openspaceaarhus/ZABLET/doc/image/bc337.jpg

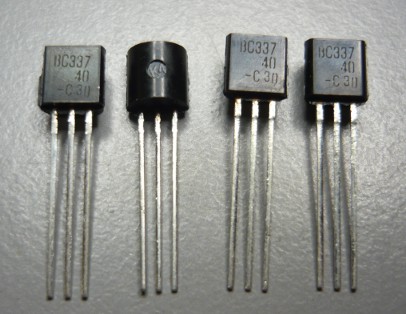
doc/image/bc337.jpg
