openspaceaarhus/ZABLET/doc/image/bc558.jpg

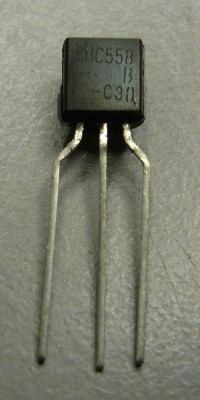
doc/image/bc558.jpg
