openspaceaarhus/ZABLET/doc/image/button.jpg

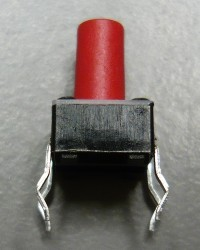
doc/image/button.jpg
