openspaceaarhus/ZABLET/doc/image/case-bottom.jpg

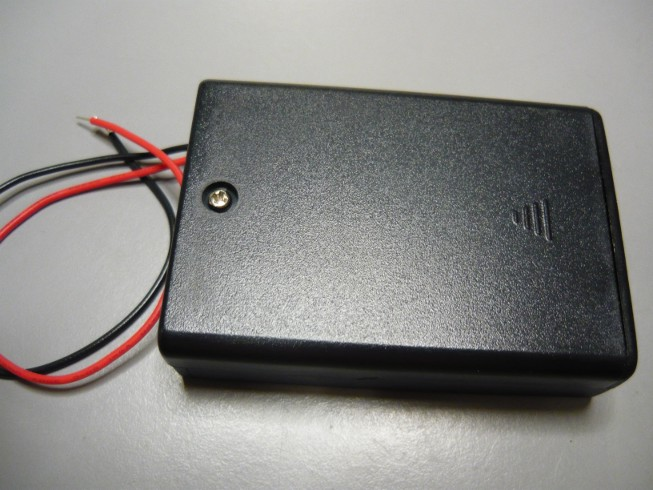
doc/image/case-bottom.jpg
