openspaceaarhus/ZABLET/doc/image/case-inside-loose.jpg

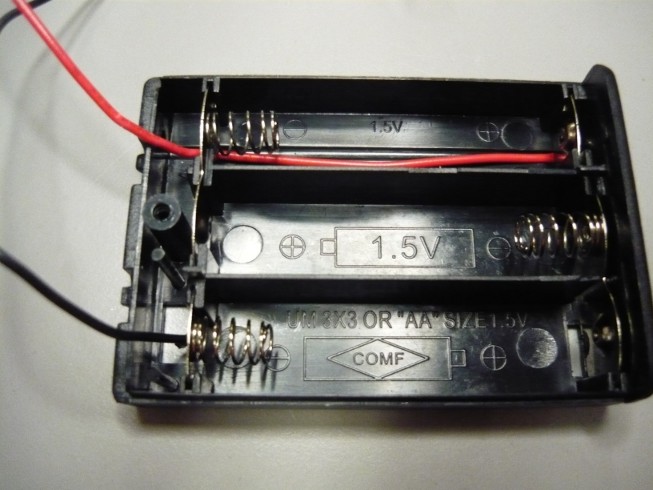
doc/image/case-inside-loose.jpg
