openspaceaarhus/ZABLET/doc/image/case-inside-orig.jpg

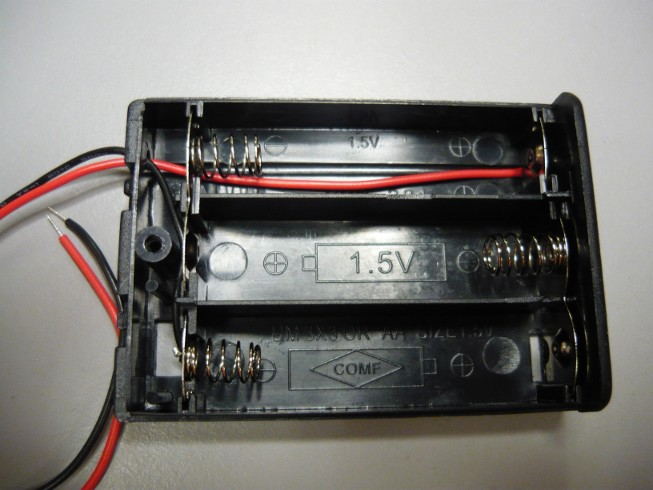
doc/image/case-inside-orig.jpg
