openspaceaarhus/ZABLET/doc/image/case-inside-rerouted.jpg

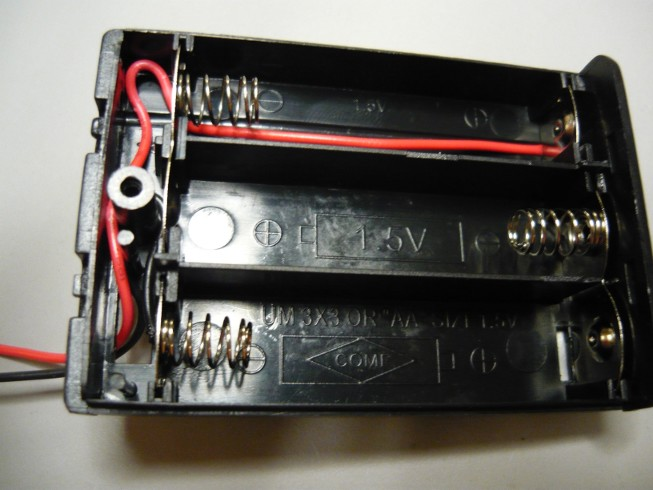
doc/image/case-inside-rerouted.jpg
