openspaceaarhus/ZABLET/doc/image/case-outside-rerouted.jpg

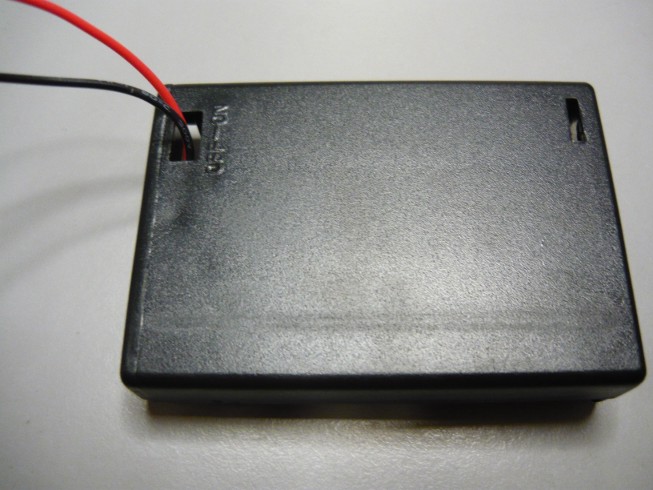
doc/image/case-outside-rerouted.jpg
