openspaceaarhus/ZABLET/doc/image/case-top.jpg

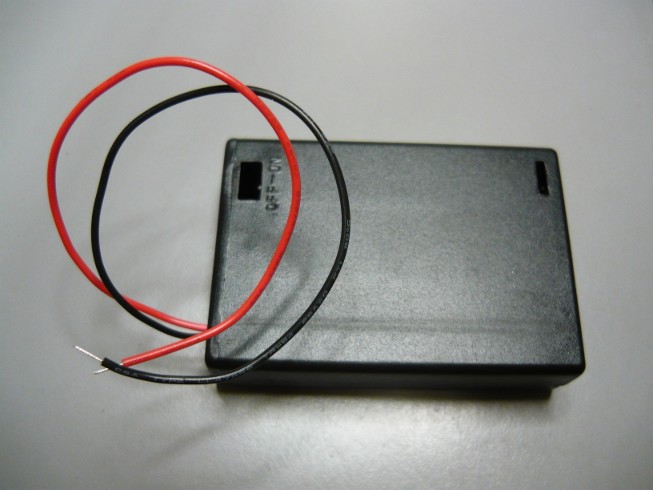
doc/image/case-top.jpg
