openspaceaarhus/ZABLET/doc/image/ceramic-caps.jpg

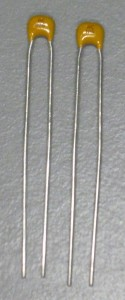
doc/image/ceramic-caps.jpg
