openspaceaarhus/ZABLET/doc/image/elco.jpg

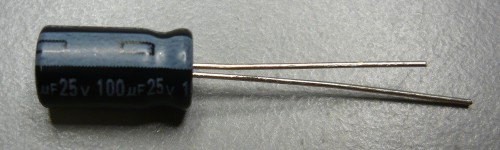
doc/image/elco.jpg
