openspaceaarhus/ZABLET/doc/image/header-6.jpg

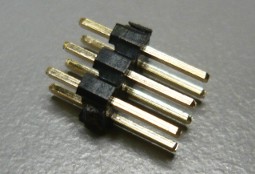
doc/image/header-6.jpg
