openspaceaarhus/ZABLET/doc/image/ir333-h0-spread.png

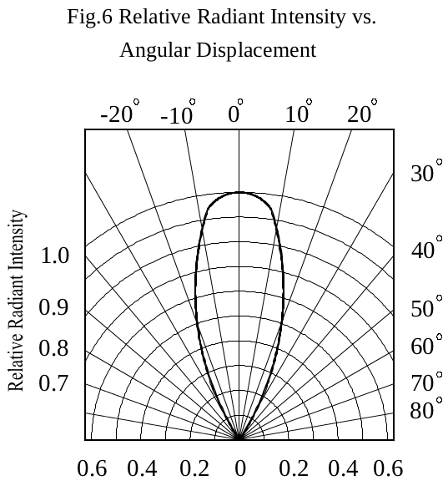
doc/image/ir333-h0-spread.png
