openspaceaarhus/ZABLET/doc/image/ir333a-spread.png

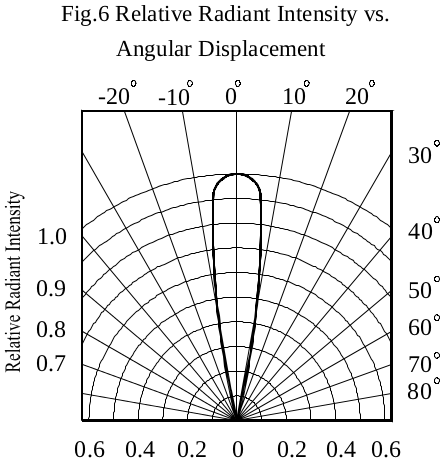
doc/image/ir333a-spread.png
