openspaceaarhus/ZABLET/doc/image/irled-10gr.jpg

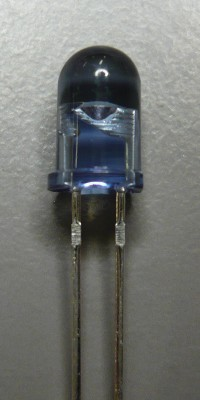
doc/image/irled-10gr.jpg
