openspaceaarhus/ZABLET/doc/image/irled-30gr.jpg

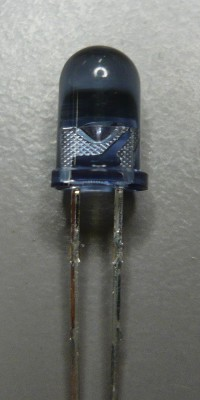
doc/image/irled-30gr.jpg
