openspaceaarhus/ZABLET/doc/image/irleds.jpg

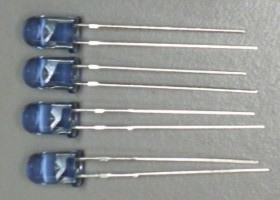
doc/image/irleds.jpg
