openspaceaarhus/ZABLET/doc/image/jumper.jpg

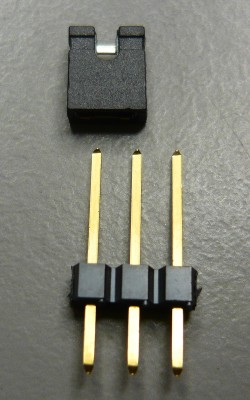
doc/image/jumper.jpg
