openspaceaarhus/ZABLET/doc/image/led-physical-dimension.png

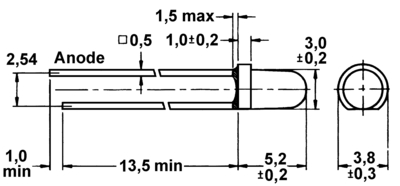
doc/image/led-physical-dimension.png
