openspaceaarhus/ZABLET/doc/image/led-through-view.png

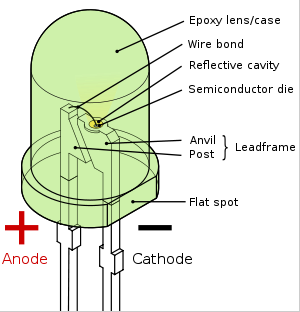
doc/image/led-through-view.png
