openspaceaarhus/ZABLET/doc/image/lodekolbe.png

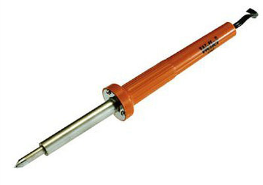
doc/image/lodekolbe.png
