openspaceaarhus/ZABLET/doc/image/modstandstabel.png

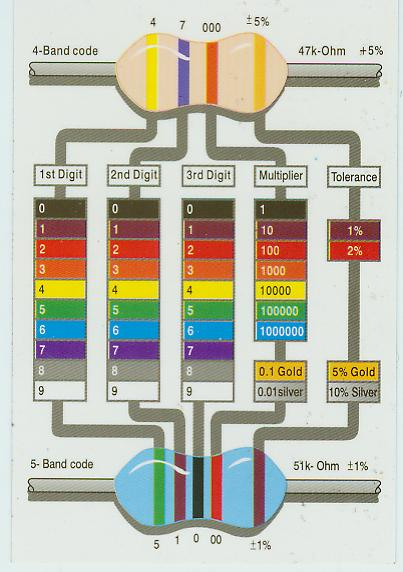
doc/image/modstandstabel.png
