openspaceaarhus/ZABLET/doc/image/osaa-loga-large.png

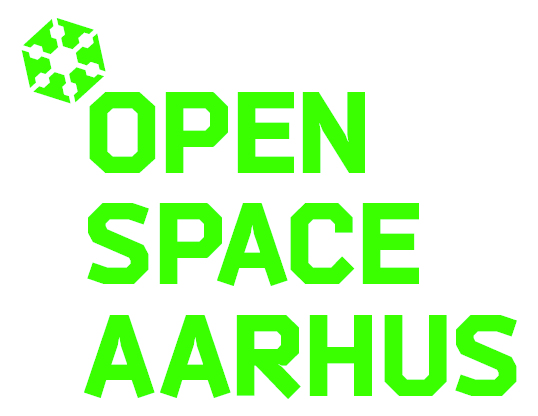
doc/image/osaa-loga-large.png
