openspaceaarhus/ZABLET/doc/image/pcb-bottom.jpg

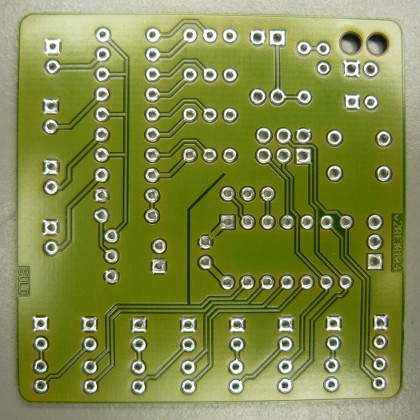
doc/image/pcb-bottom.jpg
