openspaceaarhus/ZABLET/doc/image/pcb-top.jpg

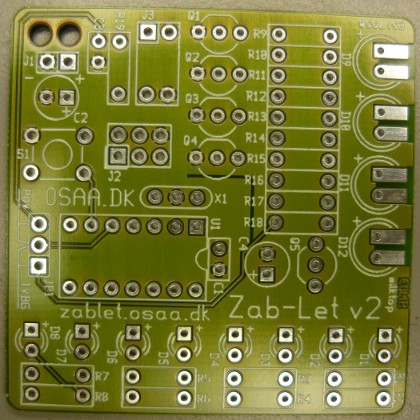
doc/image/pcb-top.jpg
