openspaceaarhus/ZABLET/doc/image/pov-cyanodrop.jpg

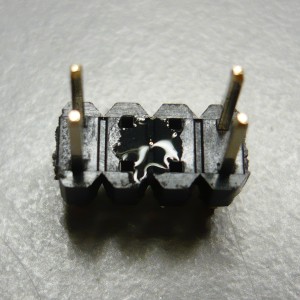
doc/image/pov-cyanodrop.jpg
