openspaceaarhus/ZABLET/doc/image/pov-elements2.jpg

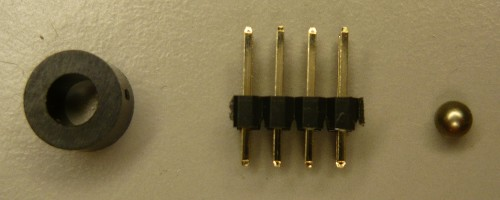
doc/image/pov-elements2.jpg
