openspaceaarhus/ZABLET/doc/image/pov-glue1.jpg

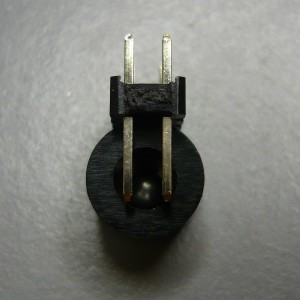
doc/image/pov-glue1.jpg
