openspaceaarhus/ZABLET/doc/image/pov-glue2.jpg

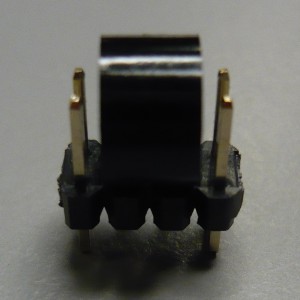
doc/image/pov-glue2.jpg
