openspaceaarhus/ZABLET/doc/image/pov-glue3.jpg

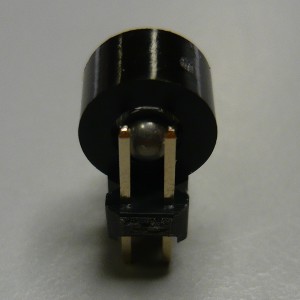
doc/image/pov-glue3.jpg
