openspaceaarhus/ZABLET/doc/image/pov-hotglue1.jpg

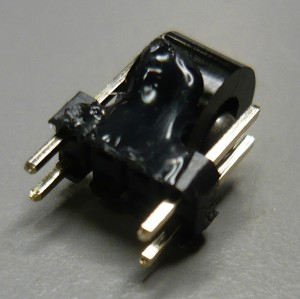
doc/image/pov-hotglue1.jpg
