openspaceaarhus/ZABLET/doc/image/pov-hotglue2.jpg

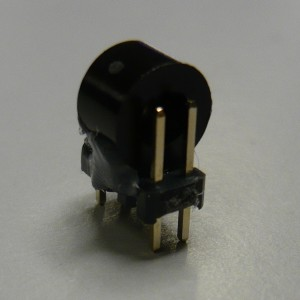
doc/image/pov-hotglue2.jpg
