openspaceaarhus/ZABLET/doc/image/pov-hotglue3.jpg

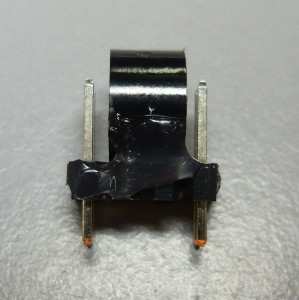
doc/image/pov-hotglue3.jpg
