openspaceaarhus/ZABLET/doc/image/pov-hotglue4.jpg

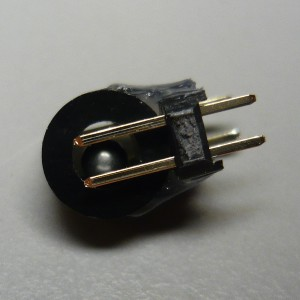
doc/image/pov-hotglue4.jpg
