openspaceaarhus/ZABLET/doc/image/pov-pick-pins.jpg

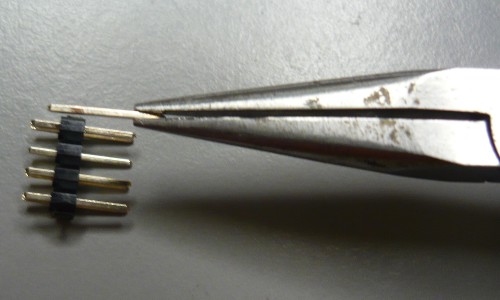
doc/image/pov-pick-pins.jpg
