openspaceaarhus/ZABLET/doc/image/pov-pins-out.jpg

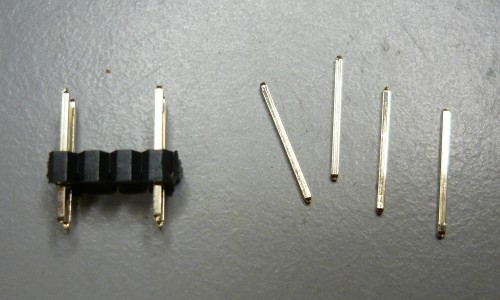
doc/image/pov-pins-out.jpg
