openspaceaarhus/ZABLET/doc/image/processor2.jpg

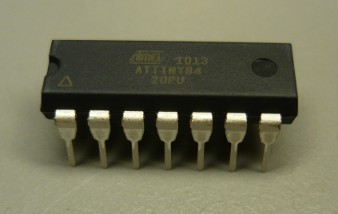
doc/image/processor2.jpg
