openspaceaarhus/ZABLET/doc/image/red-led.jpg

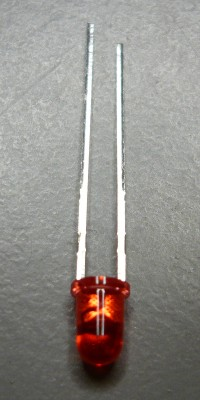
doc/image/red-led.jpg
