openspaceaarhus/ZABLET/doc/image/red-leds.jpg

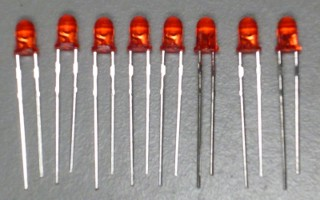
doc/image/red-leds.jpg
