openspaceaarhus/ZABLET/doc/image/resonator.jpg

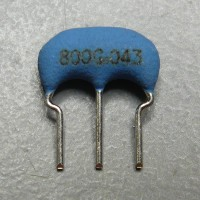
doc/image/resonator.jpg
