openspaceaarhus/ZABLET/doc/image/skaevbider.png

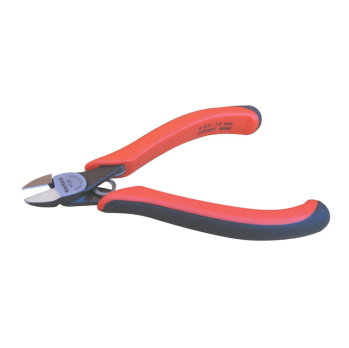
doc/image/skaevbider.png
