openspaceaarhus/ZABLET/doc/image/socket2.jpg

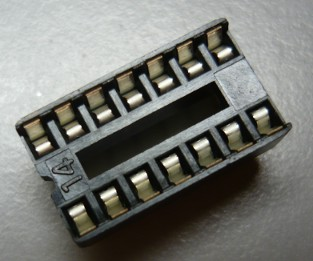
doc/image/socket2.jpg
