openspaceaarhus/ZABLET/doc/image/symbol-capacitor.png

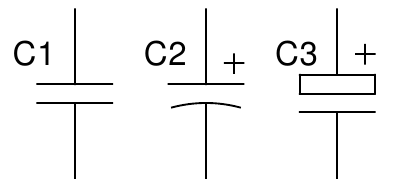
doc/image/symbol-capacitor.png
