openspaceaarhus/ZABLET/doc/image/symbol-resistor.png

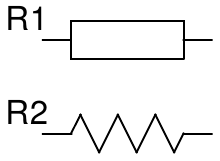
doc/image/symbol-resistor.png
