openspaceaarhus/ZABLET/doc/image/symbol-transistor.png

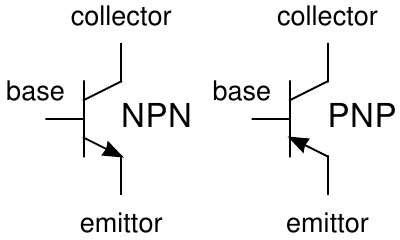
doc/image/symbol-transistor.png
