openspaceaarhus/ZABLET/doc/image/tin-litze.png

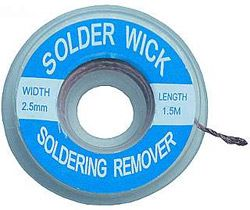
doc/image/tin-litze.png
