openspaceaarhus/ZABLET/doc/image/zablet2_sch.png

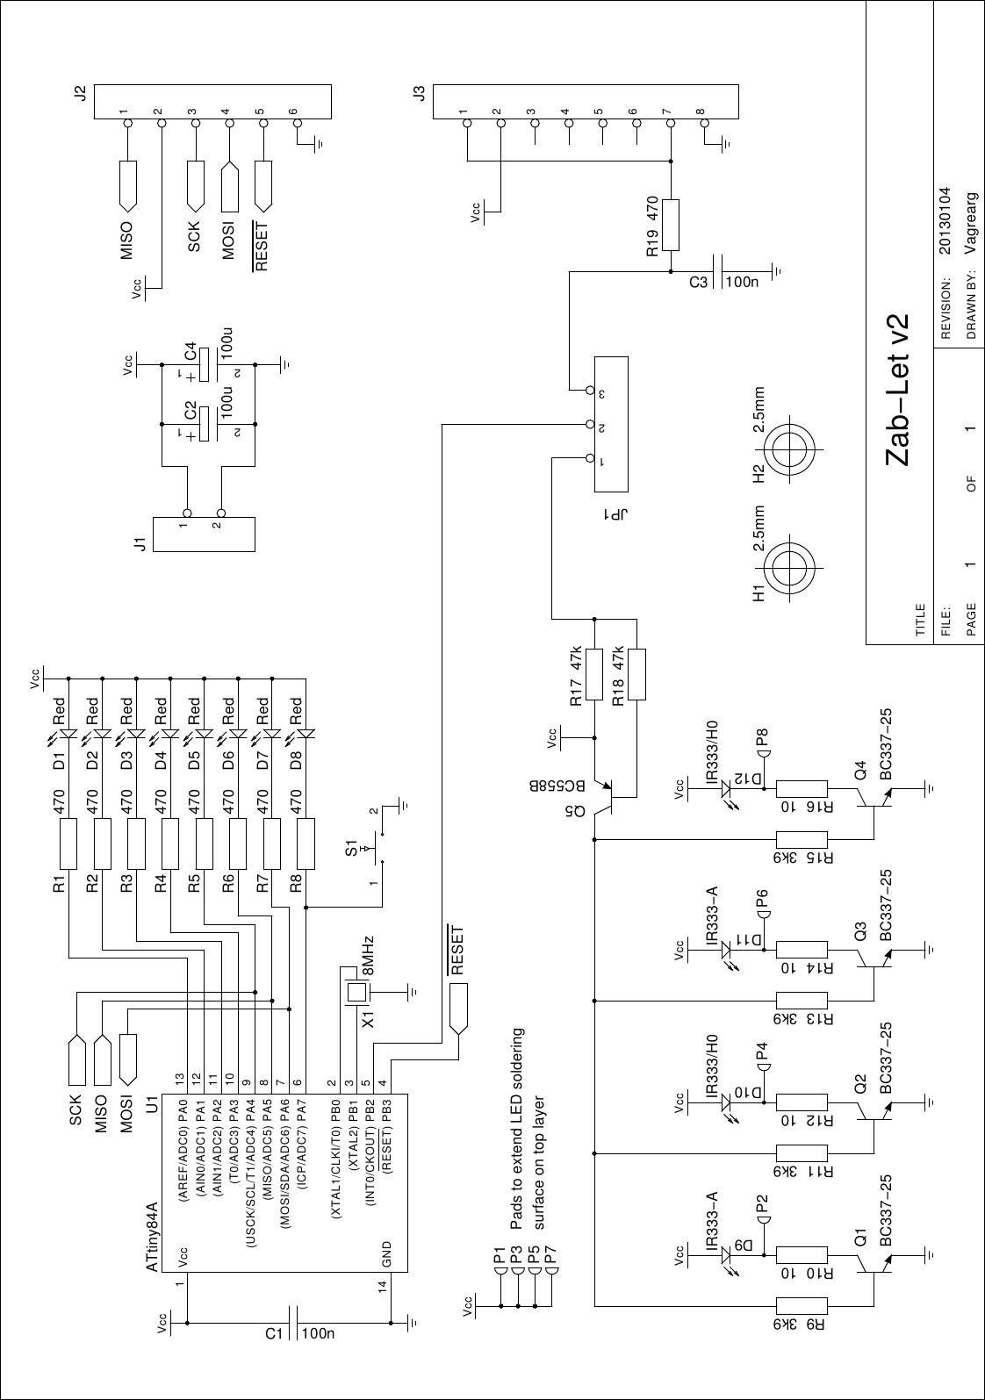
doc/image/zablet2_sch.png
