openspaceaarhus/ZABLET/doc/image/zablet-blinking-leds.png

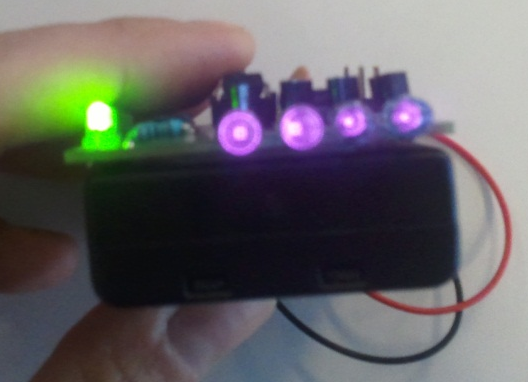
doc/image/zablet-blinking-leds.png
