openspaceaarhus/ZABLET/zablet.png

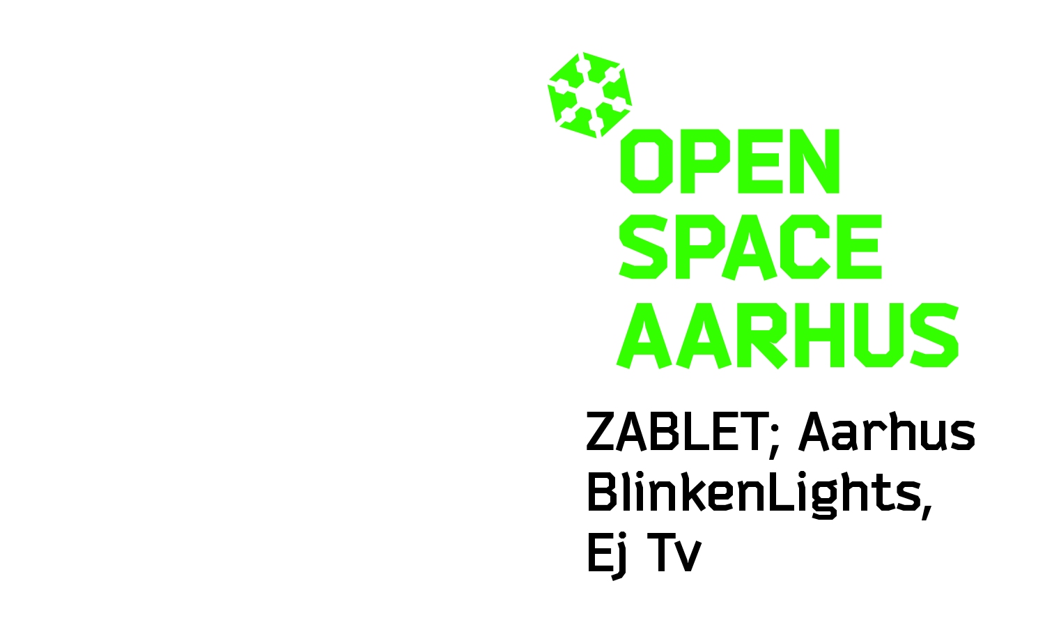
zablet.png
