openspaceaarhus/ZABLET/zabletv1/zab-let.sch

## KiCad design zabletv1/zab-let.sch (2011-08-20)

Schematic: zab-let.sch

Parts:
BT1: BATTERY
C1: 10u
C2: 100n
C3: 10n
J1: CONN_3
J2: CONN_4X2
LED1, LED2, LED3, LED4: IR_LED
LED5, LED6, LED7, LED8, LED9, LED10, LED11, LED12: LED
PROG1: CONN_3X2
Q1, Q2, Q3, Q4: BC547; TO92-CBE
Q5: BC557; TO92-CBE
R1: 47K
R2, R3, R4, R5, R6, R7, R8, R9: 125
R10: 1K
SW1: SW_PUSH
U1: ATTINY24-44-84/DIP-SO
X1: RESONATOR

Notes on the sheet:
input voltage : 4,5V nominal forward voltage: 20mA voltage drop: 2,0-2,5 set to 2V resistor= (4,5V-2V)/20mA = 125ohm
resonator with built in capacitors. Elfa: 74-702-06
Ball switch. see: http://bit.ly/98IWno
J1 is used to choose between ball-switch and IR_LED's. Both can't be connected to PB2 at once, because the debouncing capacitor on the ball-swhitch will interfere with the frequency of the LED's.
TV Begone IR LEDs
POV LEDs
