openspaceaarhus/ZABLET/firmware/adafruit-firmware-2.0/WORLDcodes.c

#include <avr/io.h>
#include <avr/pgmspace.h>
#include "main.h"

//Codes captured from Generation 3 TV-B-Gone by Limor Fried & Mitch Altman
// table of POWER codes


#ifdef NA_CODES
const uint16_t code_na000Times[] PROGMEM = {
        60, 60,
        60, 2700,
        120, 60,
        240, 60,
};
const struct IrCode code_na000Code PROGMEM = {
        freq_to_timerval(38400),
        26,             // # of pairs
        2,              // # of bits per index
        code_na000Times,
        {
                0xE2,
                0x20,
                0x80,
                0x78,
                0x88,
                0x20,
                0x10,
        }
};

const uint16_t code_na001Times[] PROGMEM = {
	50, 100,
	50, 200,
	50, 800,
	400, 400,
};
const struct IrCode code_na001Code PROGMEM = {
	freq_to_timerval(57143),
	52,		// # of pairs
	2,		// # of bits per index
	code_na001Times,  
	{
		0xD5,
		0x41,
		0x11,
		0x00,
		0x14,
		0x44,
		0x6D,
		0x54,
		0x11,
		0x10,
		0x01,
		0x44,
		0x45,
	}
};
const uint16_t code_na002Times[] PROGMEM = {
	42, 46,
	42, 133,
	42, 7519,
	347, 176,
	347, 177,
};
const struct IrCode code_na002Code PROGMEM = {
	freq_to_timerval(37037),
	100,		// # of pairs
	3,		// # of bits per index
	code_na002Times,  
	{
		0x60,
		0x80,
		0x00,
		0x00,
		0x00,
		0x08,
		0x00,
		0x00,
		0x00,
		0x20,
		0x00,
		0x00,
		0x04,
		0x12,
		0x48,
		0x04,
		0x12,
		0x48,
		0x2A,
		0x02,
		0x00,
		0x00,
		0x00,
		0x00,
		0x20,
		0x00,
		0x00,
		0x00,
		0x80,
		0x00,
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
	&code_eu131Code,
	&code_eu132Code,
	&code_eu133Code,
	&code_eu134Code,
	&code_eu135Code,
	&code_eu136Code,
	&code_eu137Code,
	&code_eu138Code,
	&code_eu139Code,
#endif
#endif
};

const uint8_t num_NAcodes = NUM_ELEM(NApowerCodes);
const uint8_t num_EUcodes = NUM_ELEM(EUpowerCodes);
